JOM52/esp32-airsens-v3/schema/airsens_solaire_s3_0.kicad_sch

## KiCad design schema/airsens_solaire_s3_0.kicad_sch (2023-06-04)

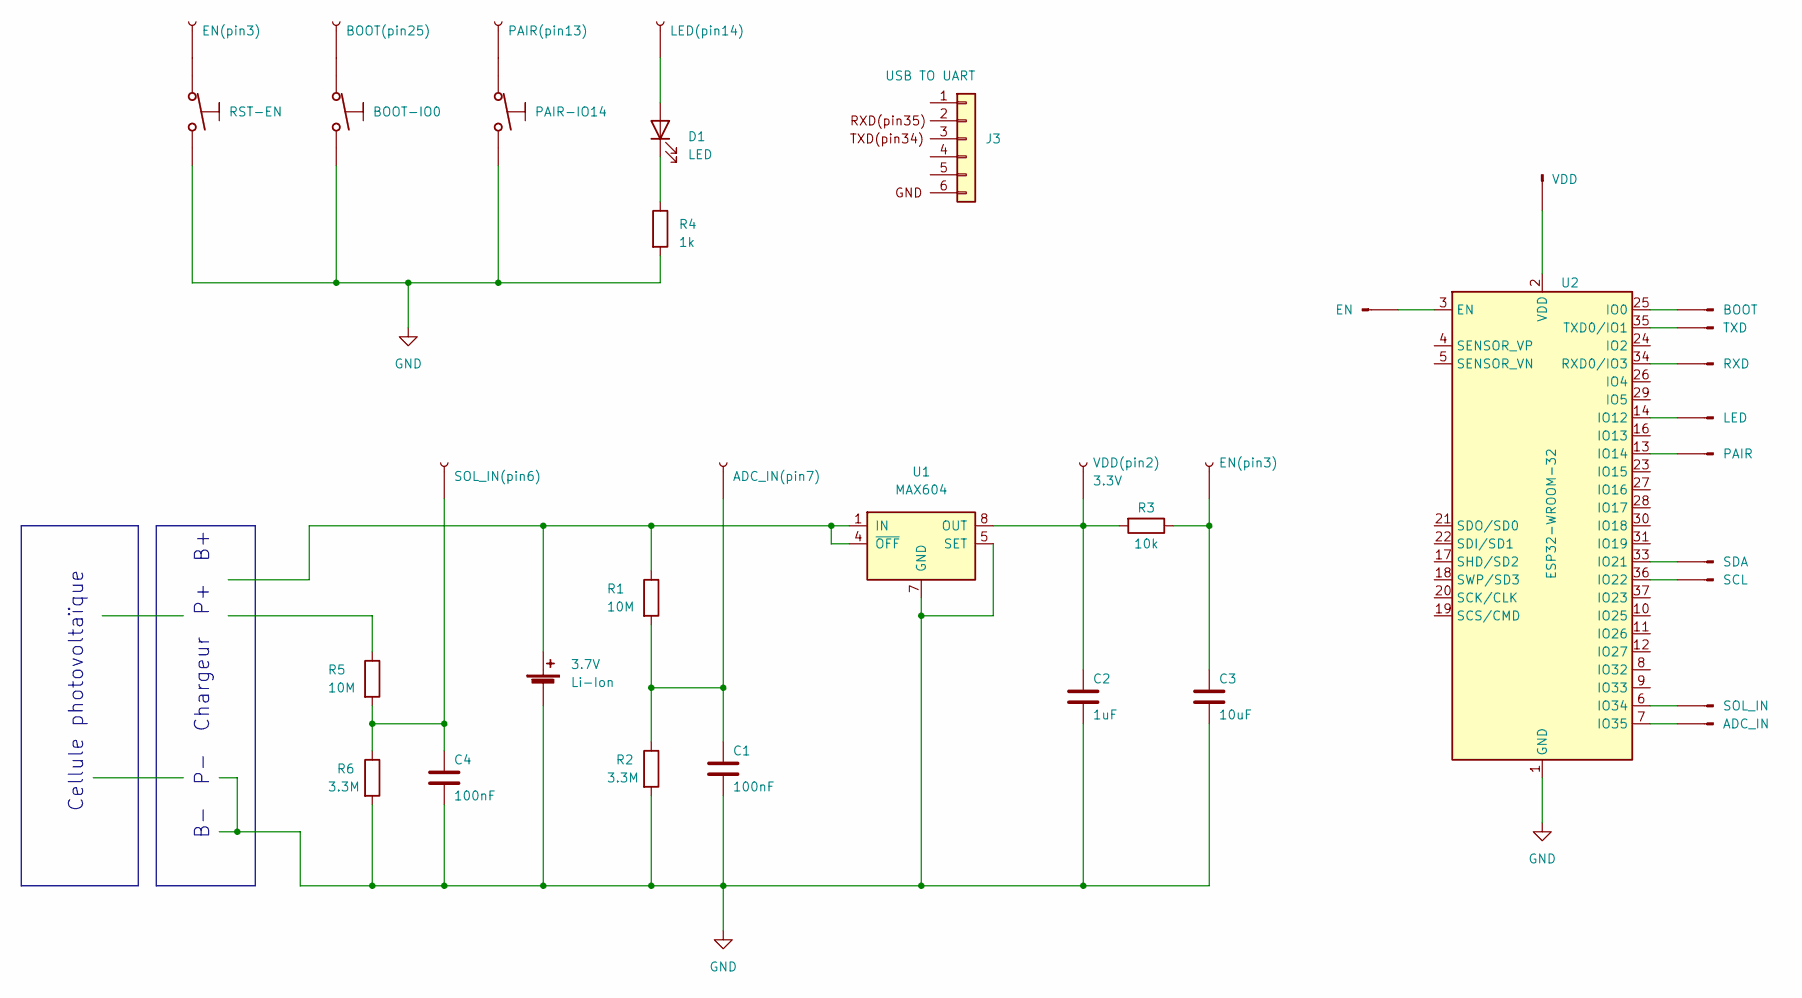
[picture p6: schematic airsens_solaire_s3_0.kicad_sch]

Parts:
3.7V: Li-Ion
BOOT(pin25): EN
C1, C4: 100nF
C2: 1uF
C3: 10uF
D1: LED
EN(pin3): EN
J1: SOL_IN(pin6)
J2: SOL_IN
J3: USB TO UART
J4: PAIR
J5: LED
LED(pin14): EN
PAIR(pin13): EN
R1, R5: 10M
R2, R6: 3.3M
R3: 10k
R4: 1k
U1: MAX604
U2: ESP32-WROOM-32
U3: PAIR-IO14; SOIC-8_3.9x4.9mm_P1.27mm
VDD(pin2): 3.3V

Connections:
GND: R4.2, U3.
unnamed: 3.7V.1 (+), R1.1, U1.1 (IN), U1.4 (~OFF)
unnamed: 3.7V.2 (-), C1.2, C2.2, C3.2, C4.2, R2.2, R6.2, U1.2 (GND), U1.3 (GND), U1.5 (SET), U1.6 (GND), U1.7 (GND)
unnamed: C1.1, R1.2, R2.1
unnamed: C2.1, R3.2, U1.8 (OUT), VDD(pin2).1
unnamed: C3.1, EN(pin3).1, R3.1
unnamed: C4.1, J1.1, R5.2, R6.1
unnamed: D1.1 (K), R4.1
unnamed: D1.2 (A), LED(pin14).1
unnamed: J2.1, U2.6 (IO34)
unnamed: J4.1, U2.13 (IO14)
unnamed: J5.1, U2.14 (IO12)
unnamed: PAIR(pin13).1, U3.
unnamed: U2.1 (GND), U2.15 (GND), U2.38 (GND), U2.39 (GND)

Notes on the sheet:
Cellule photovoltaïque
B- P- Chargeur P+ B+
